pscorbett/OCD/Mechanical/OCD panel black bg.png

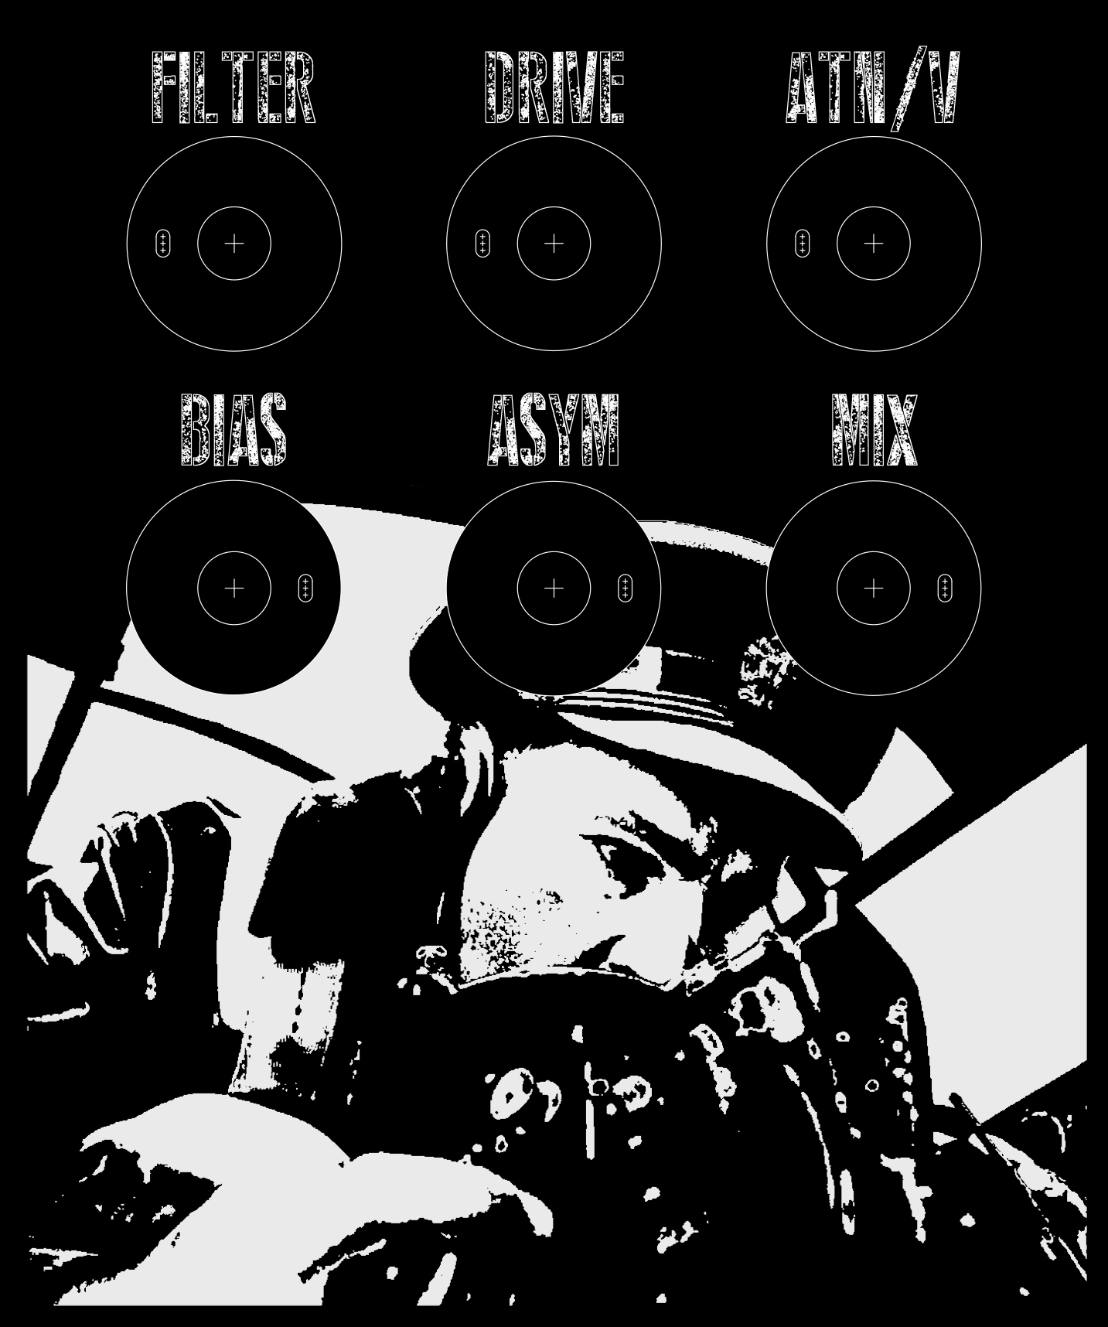
Mechanical/OCD panel black bg.png
